neggles/esp32-cantroller/EltekController/shapes3D/ESP32-S2-WROVER-I.STEP

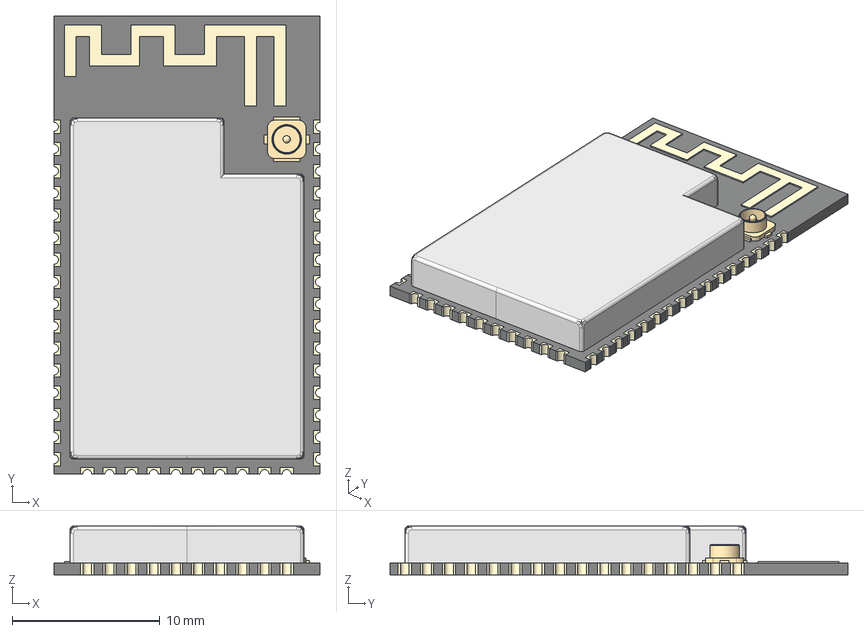
[picture p18: CAD file, 2021-04-18]
EltekController/shapes3D/ESP32-S2-WROVER-I.STEP
18.0 x 31.0 x 3.30 mm
PCB
Castellations
Trace Antenna
UFL Connector
Can
