neggles/esp32-cantroller/EltekController/shapes3D/OLED_1.3.STEP

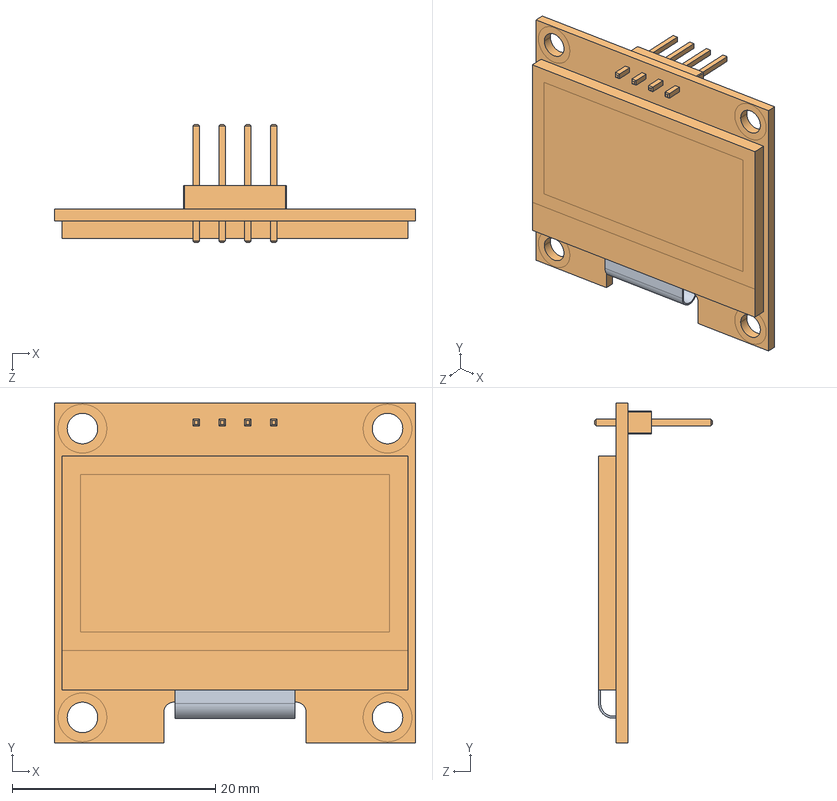
[picture p19: CAD file, 2021-04-18]
EltekController/shapes3D/OLED_1.3.STEP
35.5 x 33.4 x 11.6 mm
