neggles/esp32-cantroller/EltekController/shapes3D/R_0402_1005Metric.step

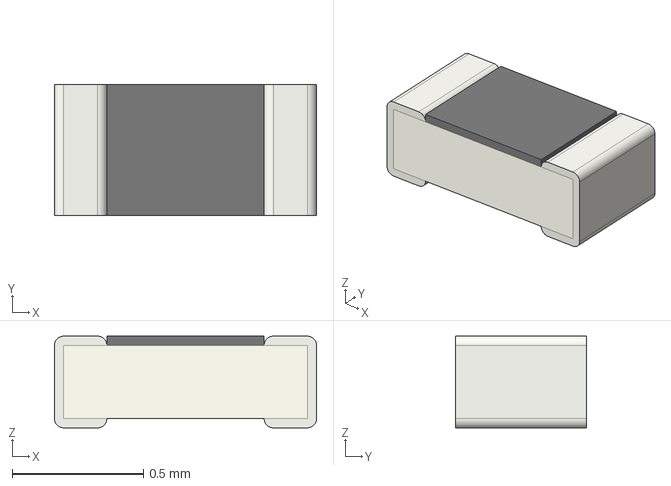
[picture p20: CAD file, 2021-04-18]
EltekController/shapes3D/R_0402_1005Metric.step
1.00 x 0.5 x 0.35 mm
