neggles/esp32-cantroller/EltekController/shapes3D/SM04B-SRSS-TB.STEP

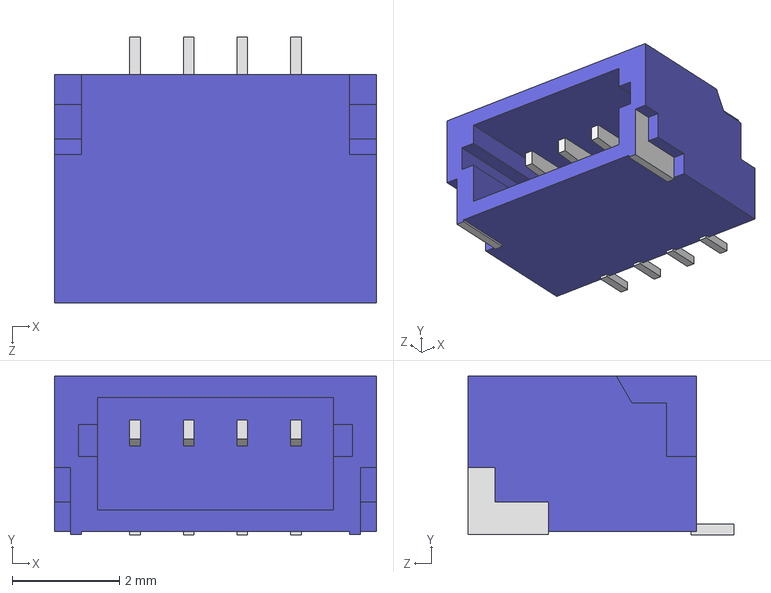
[picture p21: CAD file, 2021-04-18]
EltekController/shapes3D/SM04B-SRSS-TB.STEP
6.00 x 2.96 x 4.95 mm
