neggles/esp32-cantroller/EltekController/shapes3D/SHF-103-01-L-D-TH.stp

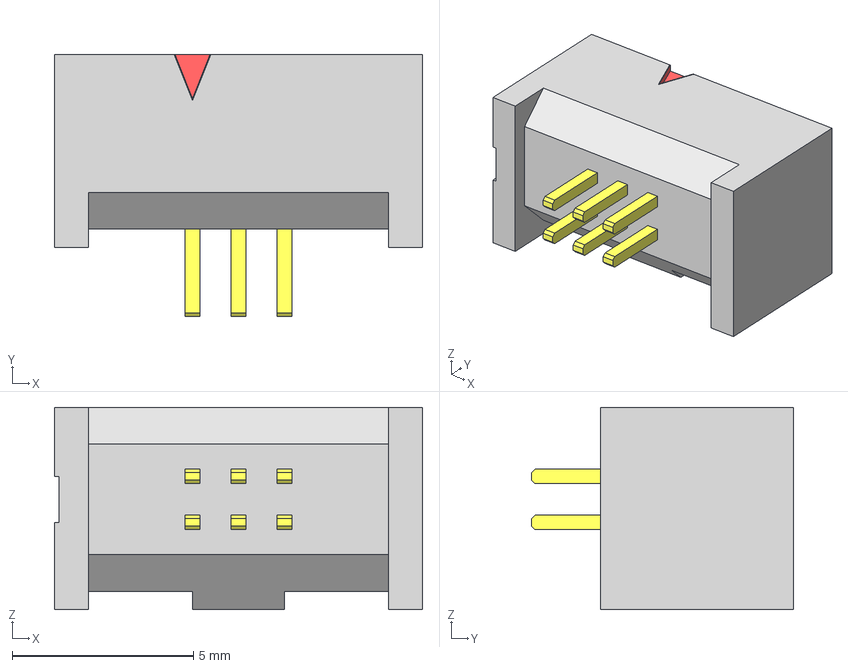
[picture p22: CAD file, 2021-04-18]
EltekController/shapes3D/SHF-103-01-L-D-TH.stp
10.2 x 7.24 x 5.59 mm
_SHF-103-01-D_header
_SHF-First_Position_Indicator
_T-1S71-02-03-D-TH
