neggles/esp32-cantroller/EltekController/shapes3D/SMD3535 RGB.stp

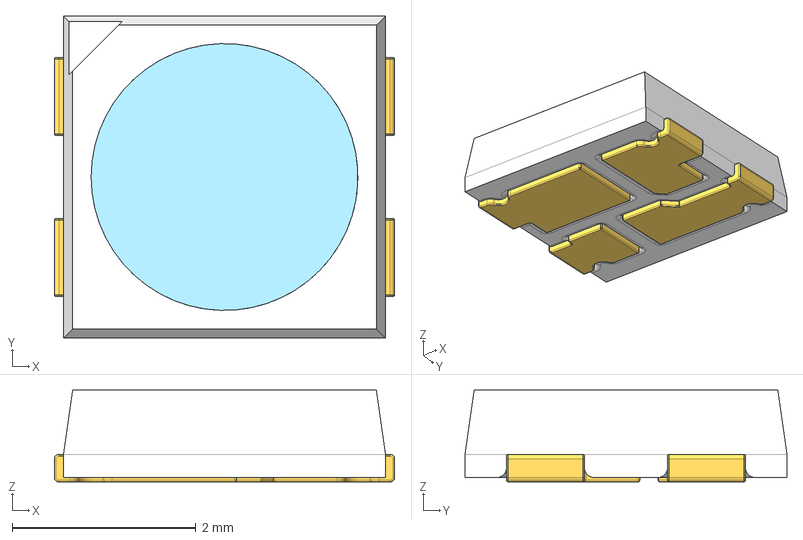
[picture p23: CAD file, 2021-04-18]
EltekController/shapes3D/SMD3535 RGB.stp
3.70 x 3.50 x 1.00 mm
