neggles/esp32-cantroller/EltekController/shapes3D/SOT-89.step

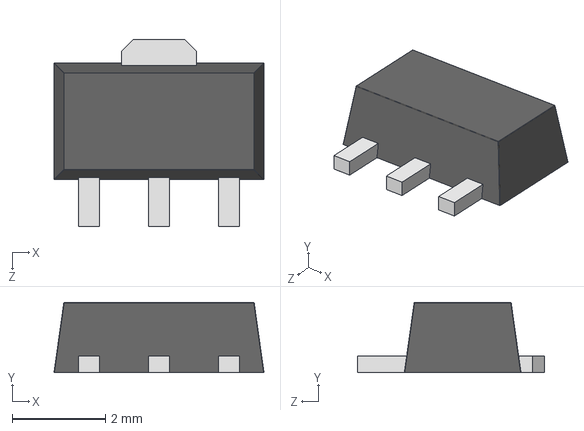
[picture p24: CAD file, 2021-04-18]
EltekController/shapes3D/SOT-89.step
4.50 x 1.50 x 4.00 mm
