neggles/esp32-cantroller/EltekController/shapes3D/SOD123.step

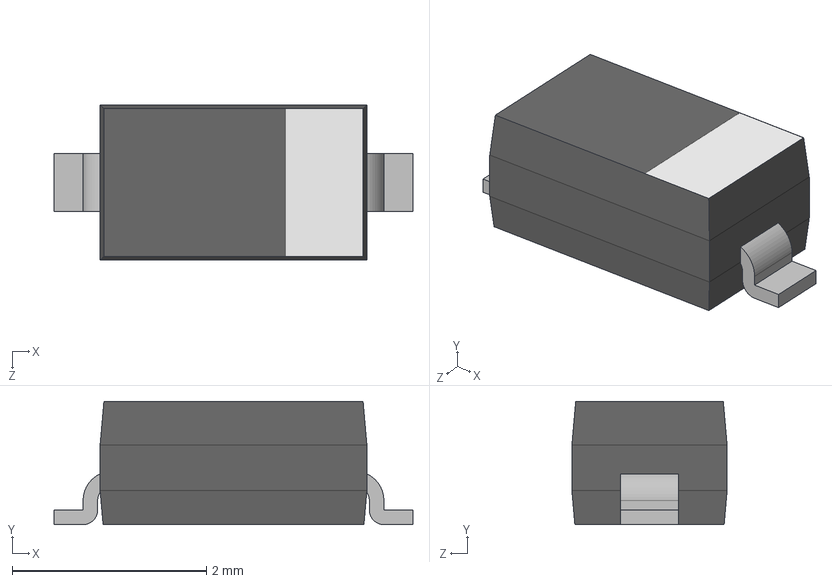
[picture p25: CAD file, 2021-04-18]
EltekController/shapes3D/SOD123.step
3.70 x 1.27 x 1.60 mm
