neggles/esp32-cantroller/EltekController/shapes3D/CON_TE_5-103634-3.stp

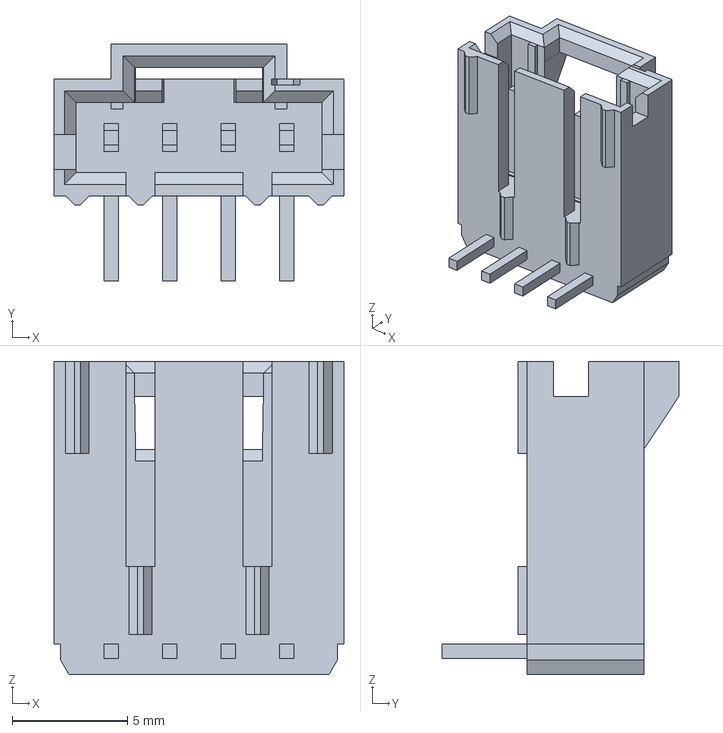
[picture p26: CAD file, 2021-04-18]
EltekController/shapes3D/CON_TE_5-103634-3.stp
12.6 x 10.3 x 13.6 mm
